braillerap/OpenStreetTangible/docs/IMG/Export_option_polygone_traces_inactive.png

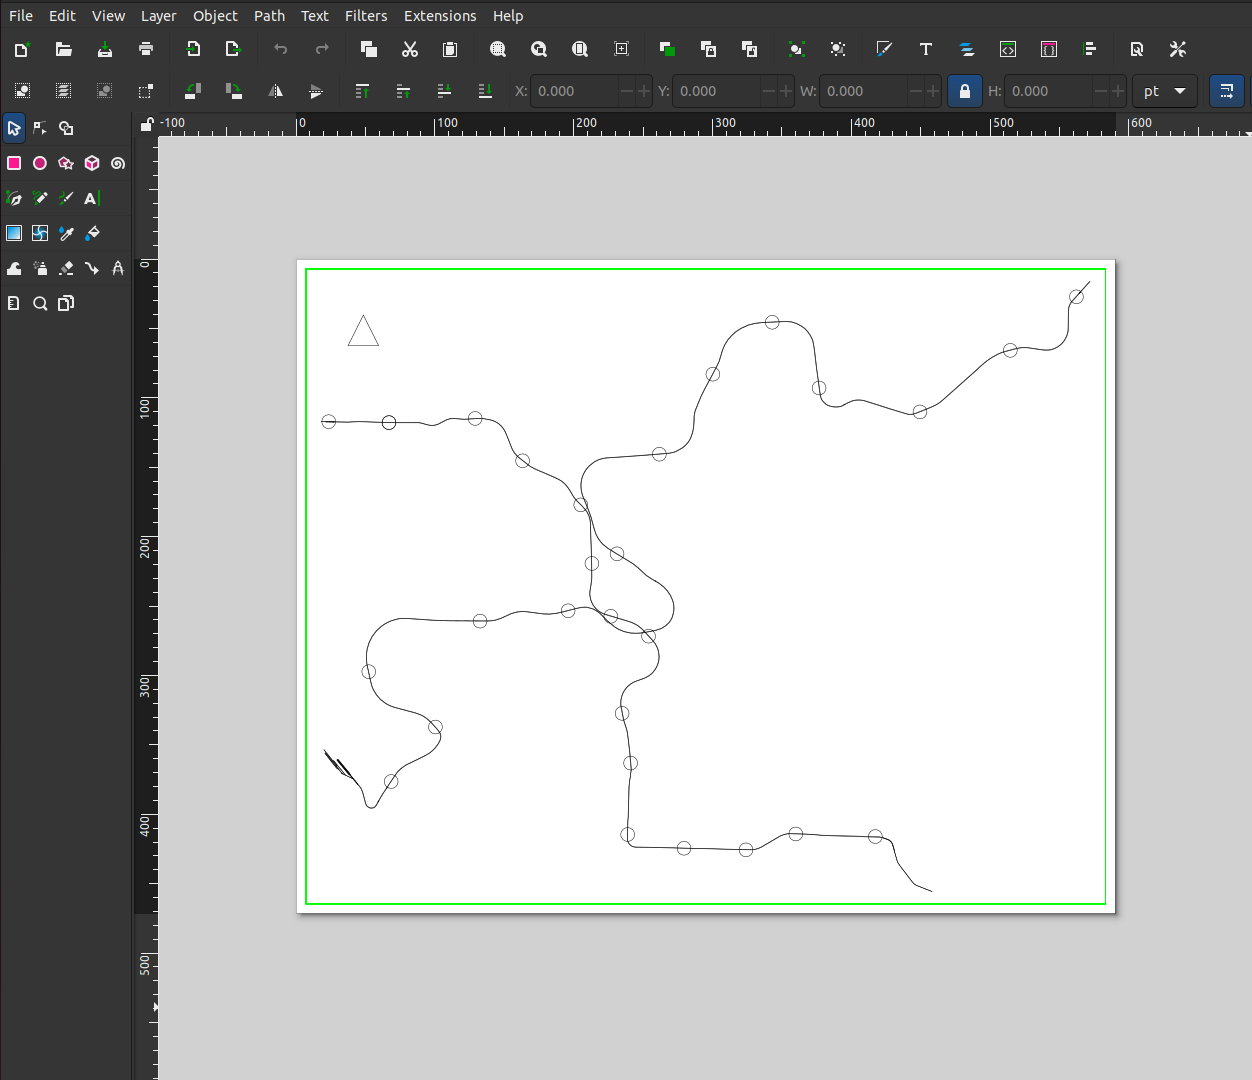
docs/IMG/Export_option_polygone_traces_inactive.png
