braillerap/OpenStreetTangible/docs/IMG/Export_option_polygone_traces_lignes_active.png

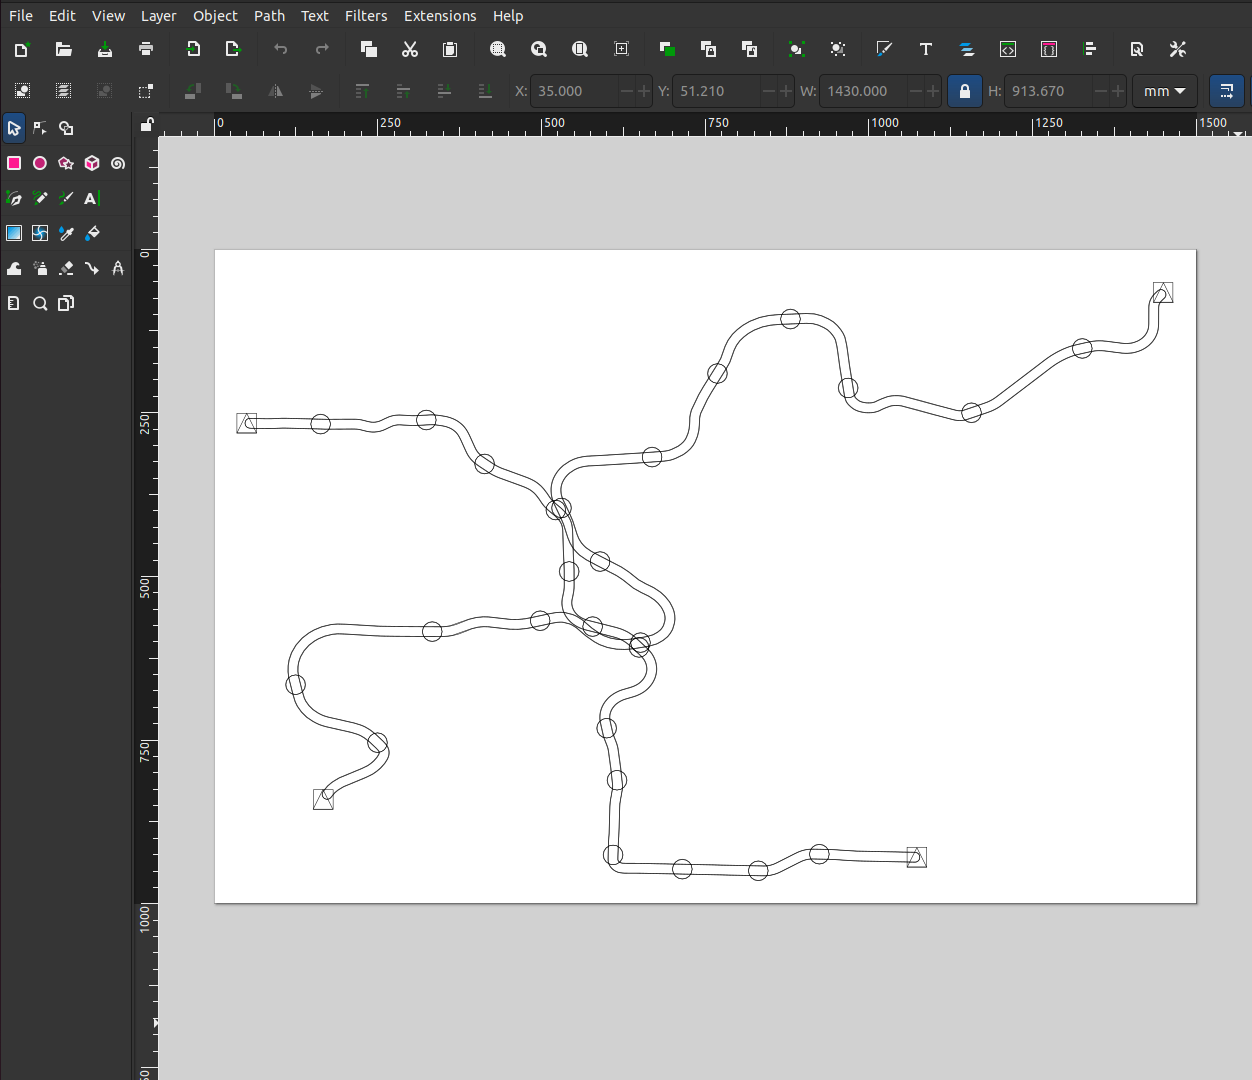
docs/IMG/Export_option_polygone_traces_lignes_active.png
