braillerap/OpenStreetTangible/docs/IMG/gravure_et_percage_plan_global_laser.jpg

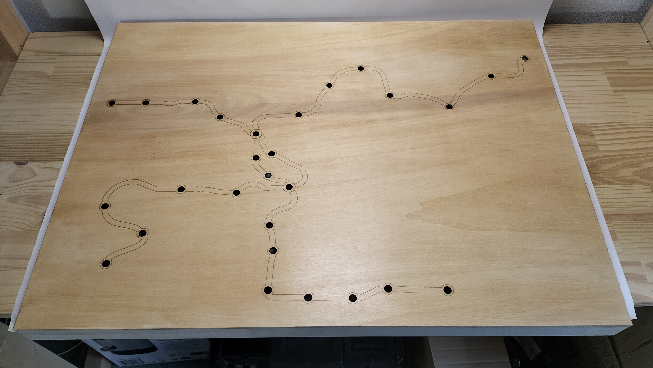
docs/IMG/gravure_et_percage_plan_global_laser.jpg
