braillerap/OpenStreetTangible/docs/IMG/label2.jpg

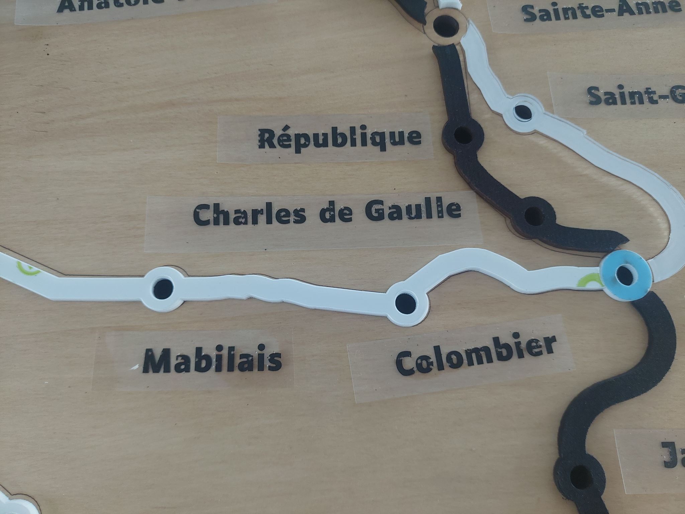
docs/IMG/label2.jpg
