braillerap/OpenStreetTangible/docs/IMG/lignes_decoupees.jpg

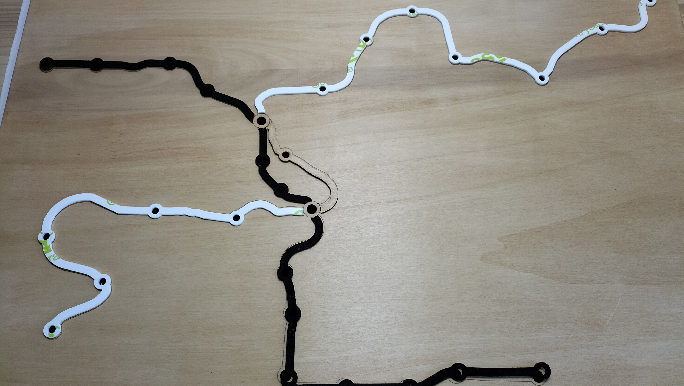
docs/IMG/lignes_decoupees.jpg
