braillerap/OpenStreetTangible/docs/IMG/prepa_bouton_connecteur.jpg

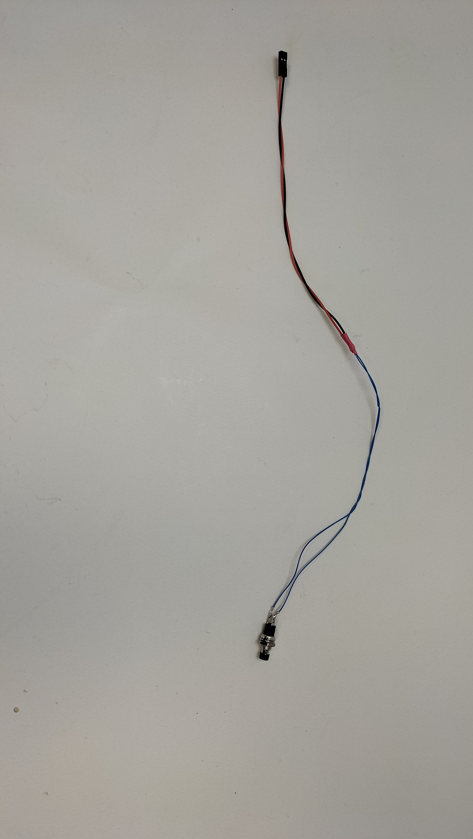
docs/IMG/prepa_bouton_connecteur.jpg
