braillerap/OpenStreetTangible/docs/IMG/prepa_bouton_connecteur_contraste.jpg

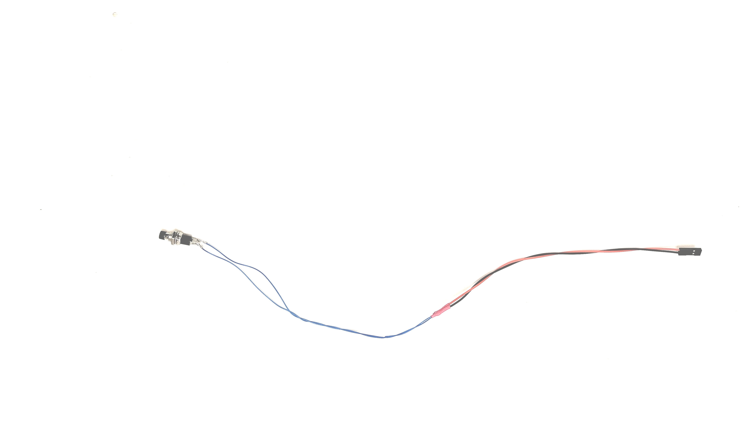
docs/IMG/prepa_bouton_connecteur_contraste.jpg
